kreme123/Verdant02/FirmwareVIAL/verdant02/keymaps/vial/config.h

/* SPDX-License-Identifier: GPL-2.0-or-later */

#pragma once

#define VIAL_KEYBOARD_UID {0x95, 0x4C, 0xAE, 0x1C, 0x68, 0xED, 0x99, 0xE1}
#define VIAL_UNLOCK_COMBO_ROWS {0, 1}
#define VIAL_UNLOCK_COMBO_COLS {0, 1}
#define DYNAMIC_KEYMAP_LAYER_COUNT 3
